OldETC/Bipedal_Qubie/faces/Untitled 1.gif

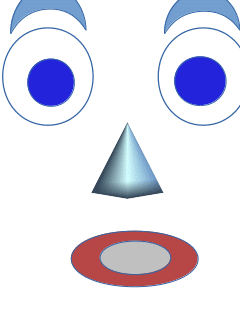
faces/Untitled 1.gif
