OldETC/Bipedal_Qubie/Qubie_code/python/faceClose.jpg

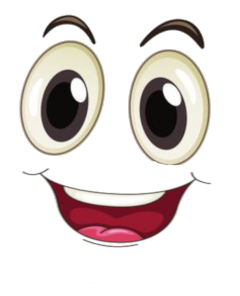
Qubie_code/python/faceClose.jpg
