OldETC/Bipedal_Qubie/qubie/stl/microgripper/connector.stl

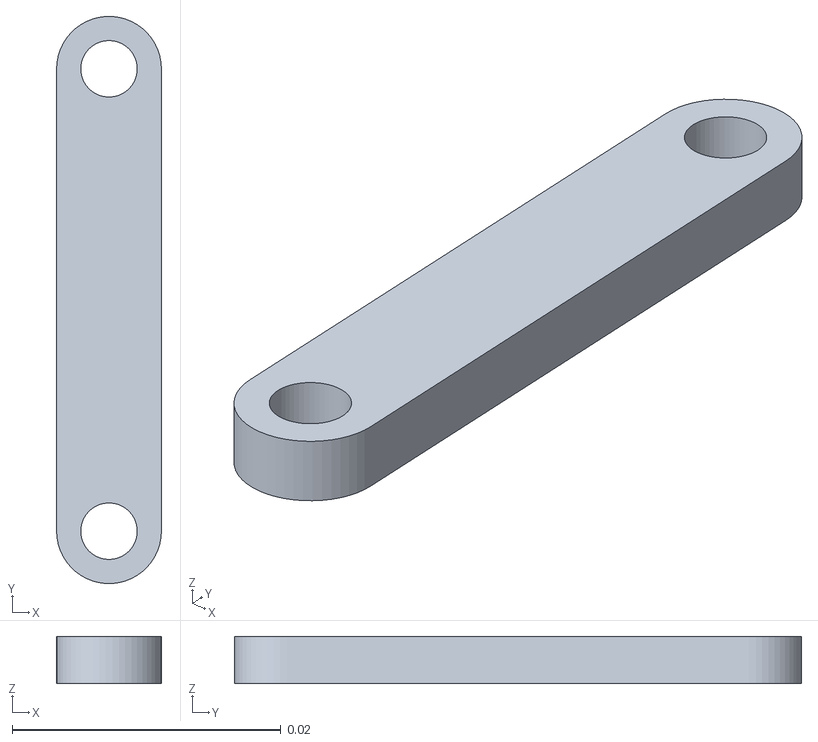
[picture p17: CAD file, 2021-06-25]
qubie/stl/microgripper/connector.stl
0.0078 x 0.0422 x 0.0035
