OldETC/Bipedal_Qubie/qubie/stl/minigripper/mybase.stl

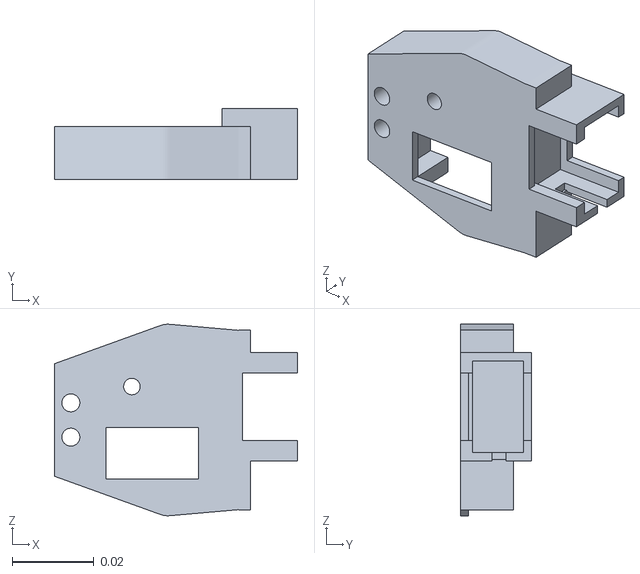
[picture p18: CAD file, 2021-06-25]
qubie/stl/minigripper/mybase.stl
0.0595 x 0.0174 x 0.0469
