OldETC/Bipedal_Qubie/PrintDesign/minigripper/minigripper/files/Connector.stl

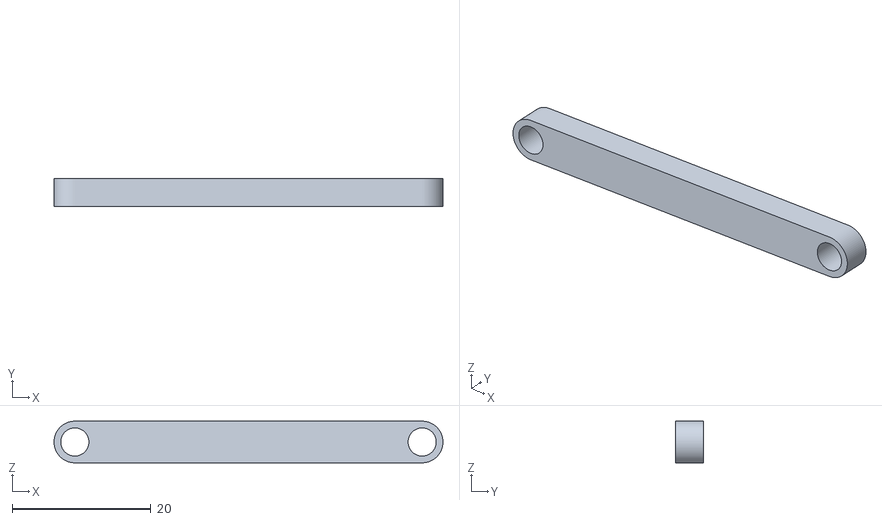
[picture p19: CAD file, 2021-06-24]
PrintDesign/minigripper/minigripper/files/Connector.stl
56.0 x 4.00 x 6.00
