OldETC/Bipedal_Qubie/qubie/stl/footassembly/shoe.stl

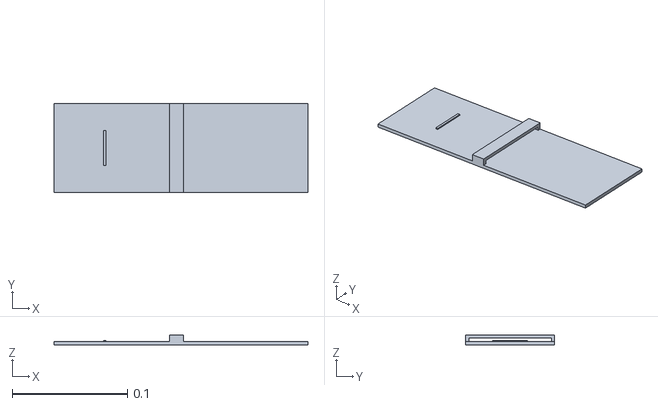
[picture p20: CAD file, 2021-06-25]
qubie/stl/footassembly/shoe.stl
0.22 x 0.0767 x 0.009
