OldETC/Bipedal_Qubie/qubie/stl/head/Neckclamp.stl

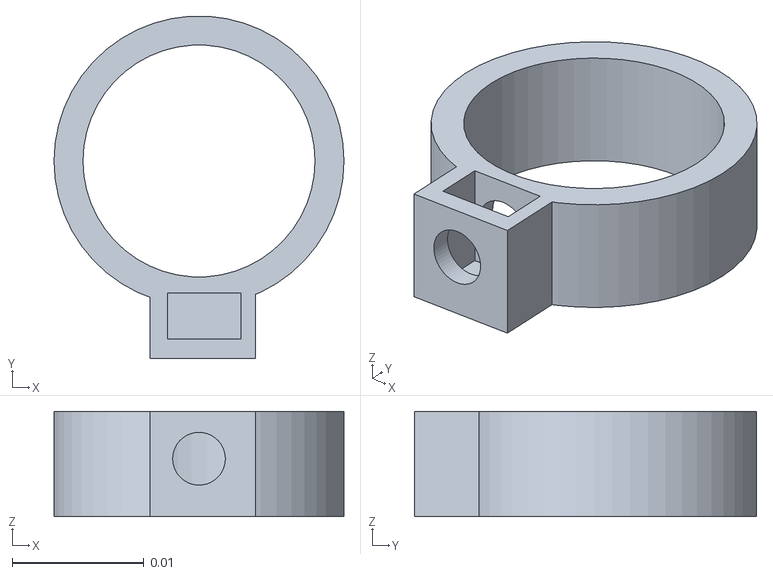
[picture p21: CAD file, 2021-06-25]
qubie/stl/head/Neckclamp.stl
0.022 x 0.026 x 0.008
