OldETC/Bipedal_Qubie/qubie/stl/microgripper/MountingPlate.stl

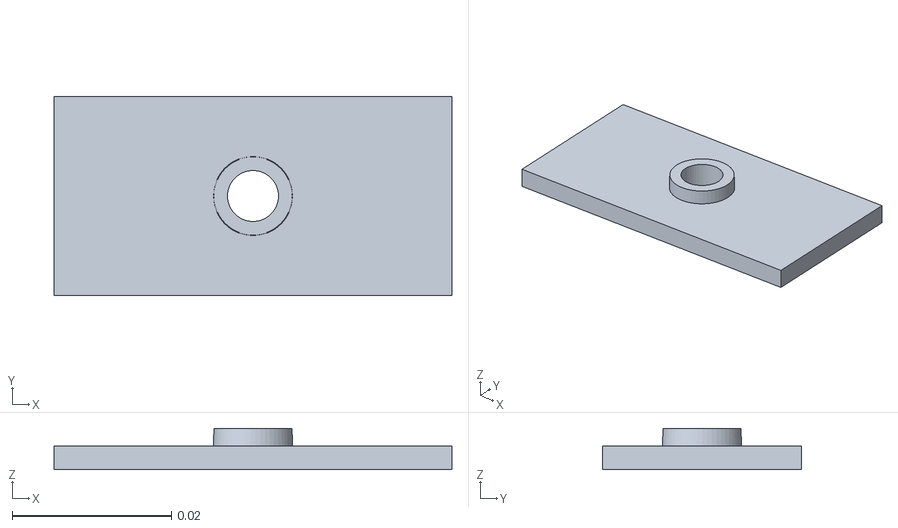
[picture p22: CAD file, 2021-06-25]
qubie/stl/microgripper/MountingPlate.stl
0.05 x 0.025 x 0.0052
