OldETC/Bipedal_Qubie/qubie/stl/minigripper/myminiclaw.stl

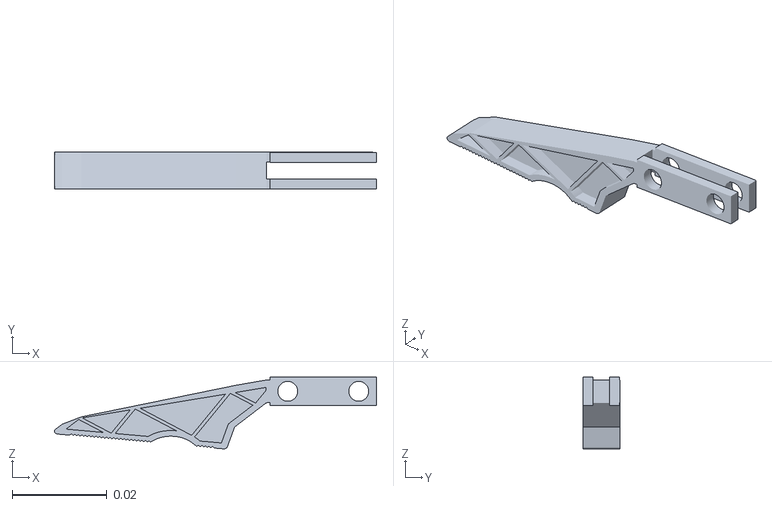
[picture p23: CAD file, 2021-06-25]
qubie/stl/minigripper/myminiclaw.stl
0.068 x 0.00774 x 0.0152
