OldETC/Bipedal_Qubie/PrintDesign/minigripper/minigripper/files/Base_AR2.stl

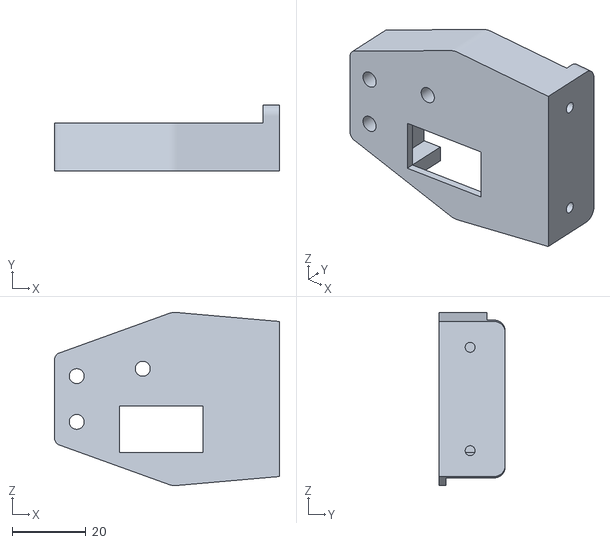
[picture p24: CAD file, 2021-06-24]
PrintDesign/minigripper/minigripper/files/Base_AR2.stl
61.0 x 18.0 x 46.9
