OldETC/Bipedal_Qubie/qubie/stl/gazeboLeftShoulderCrank.stl

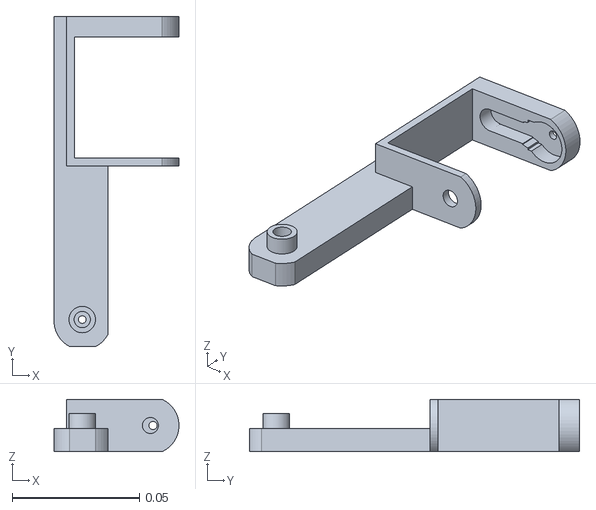
[picture p25: CAD file, 2021-06-25]
qubie/stl/gazeboLeftShoulderCrank.stl
0.0491 x 0.13 x 0.0205
