OldETC/Bipedal_Qubie/qubie/stl/head/Display.stl

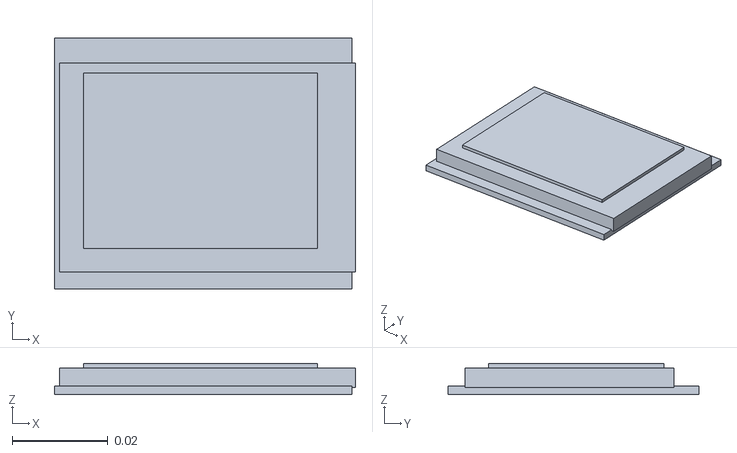
[picture p26: CAD file, 2021-06-25]
qubie/stl/head/Display.stl
0.063 x 0.0525 x 0.0065
