OldETC/Bipedal_Qubie/qubie/stl/minigripper/pivotplate.stl

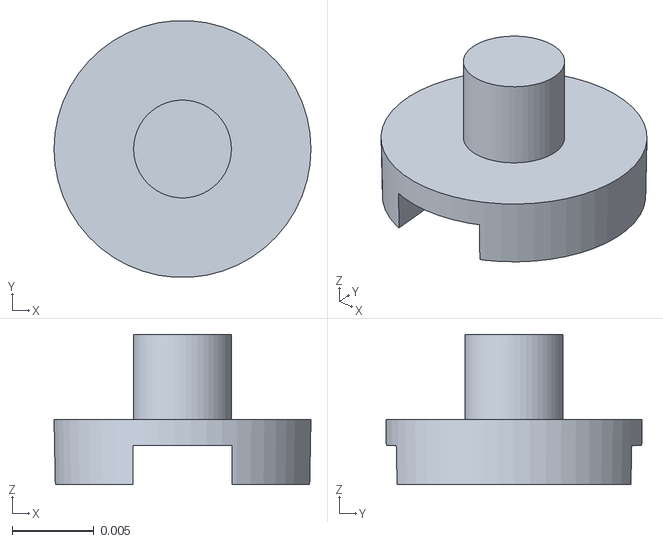
[picture p27: CAD file, 2021-06-25]
qubie/stl/minigripper/pivotplate.stl
0.0158 x 0.0157 x 0.0092
