OldETC/Bipedal_Qubie/qubie/stl/footassembly/gazeboRighttAnkleTilt.stl

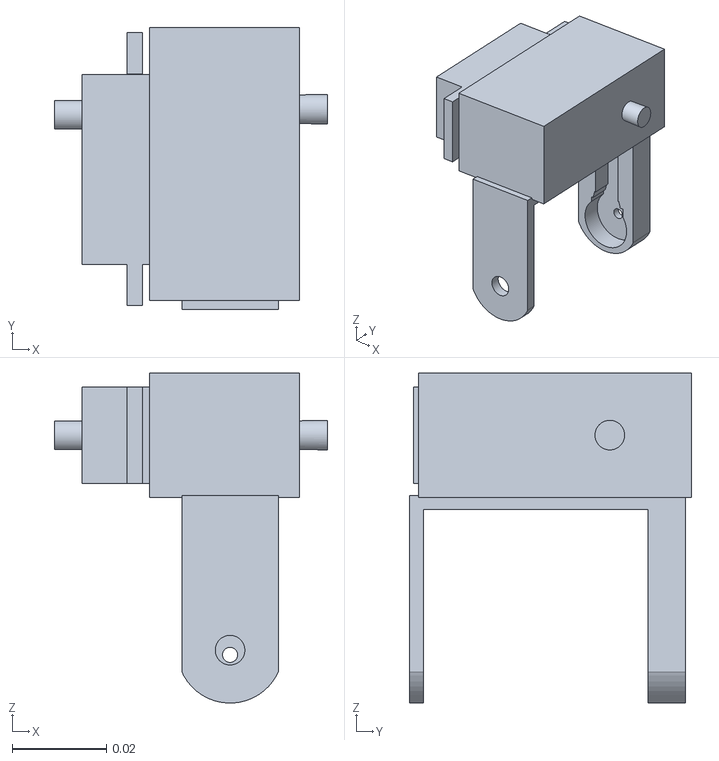
[picture p28: CAD file, 2021-06-25]
qubie/stl/footassembly/gazeboRighttAnkleTilt.stl
0.0581 x 0.06 x 0.0701
