OldETC/Bipedal_Qubie/qubie/stl/gazeboServoNbracket.stl

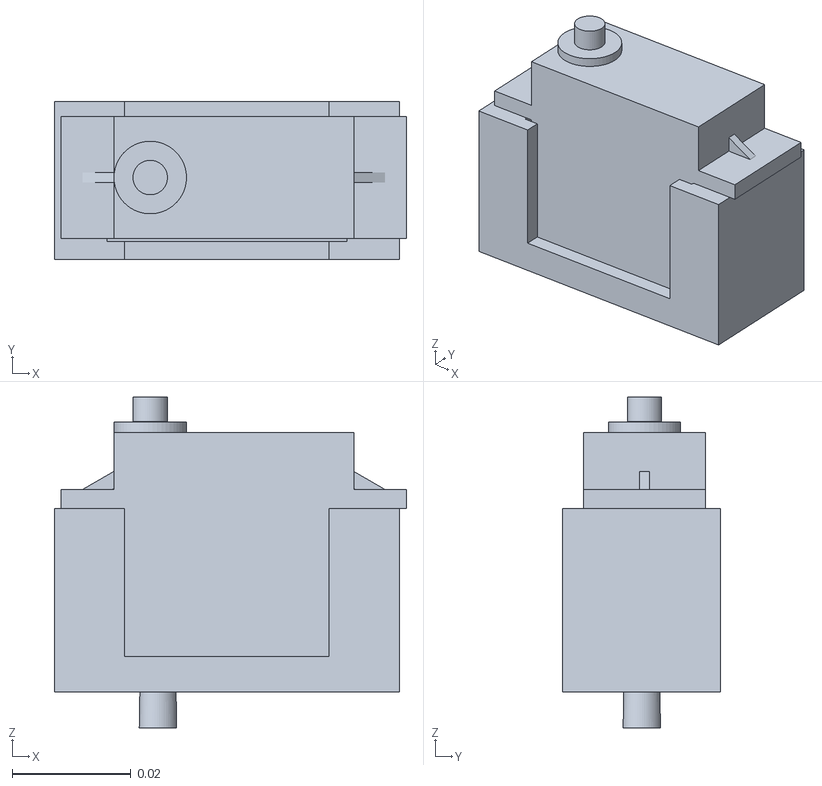
[picture p29: CAD file, 2021-06-25]
qubie/stl/gazeboServoNbracket.stl
0.0592 x 0.0265 x 0.0556
