OldETC/Bipedal_Qubie/qubie/stl/head/SpinPlatform.stl

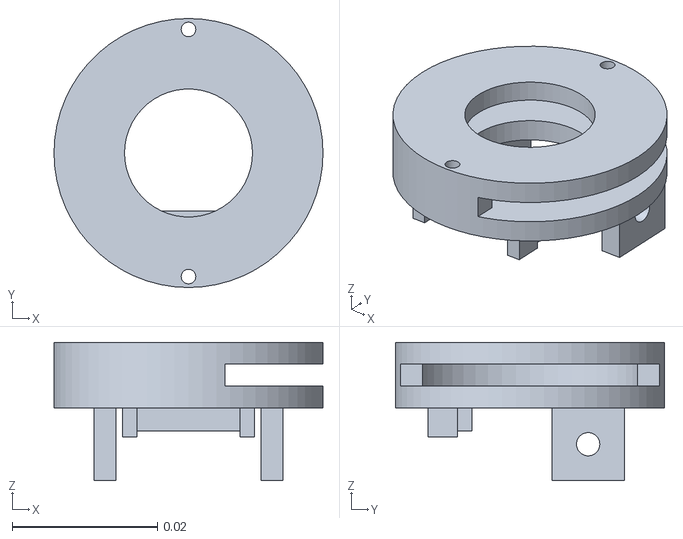
[picture p30: CAD file, 2021-06-25]
qubie/stl/head/SpinPlatform.stl
0.037 x 0.037 x 0.019
