OldETC/Bipedal_Qubie/qubie/stl/microgripper/PivotPlateCap.stl

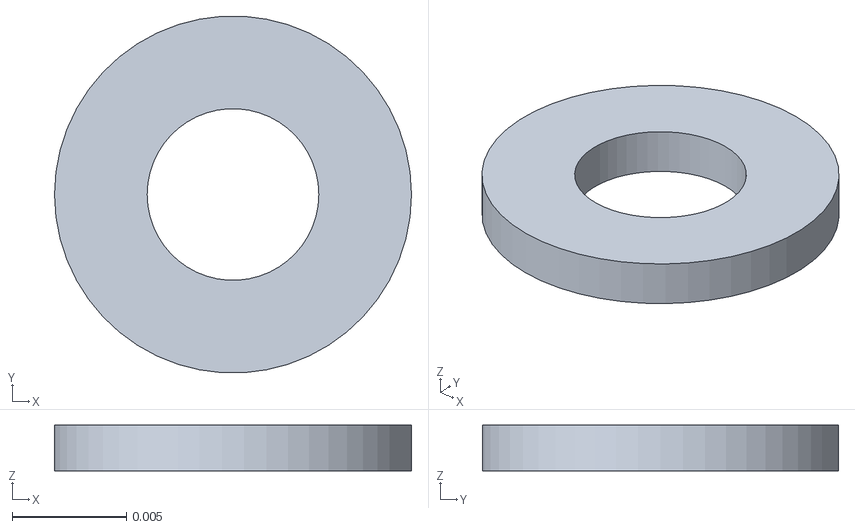
[picture p31: CAD file, 2021-06-25]
qubie/stl/microgripper/PivotPlateCap.stl
0.0156 x 0.0156 x 0.002
