OldETC/Bipedal_Qubie/qubie/stl/minigripper/myclaw.stl

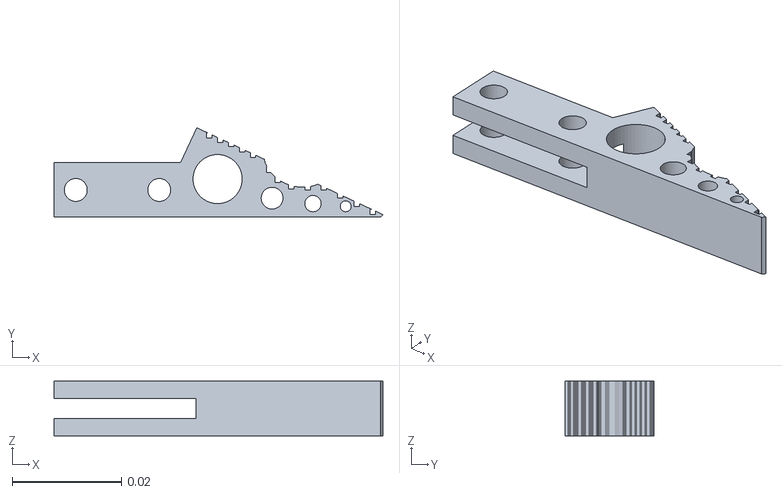
[picture p32: CAD file, 2021-06-25]
qubie/stl/minigripper/myclaw.stl
0.0603 x 0.0164 x 0.01
