OldETC/Bipedal_Qubie/qubie/stl/footassembly/robotFoot.stl

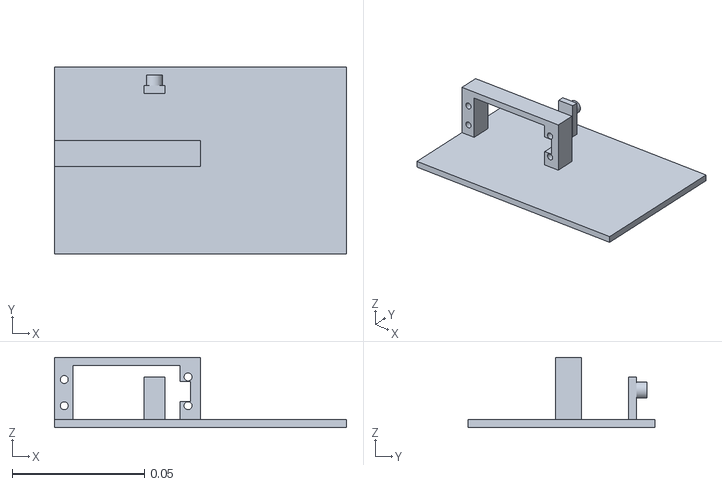
[picture p33: CAD file, 2021-06-25]
qubie/stl/footassembly/robotFoot.stl
0.11 x 0.0707 x 0.0266
