OldETC/Bipedal_Qubie/qubie/stl/head/headBack.stl

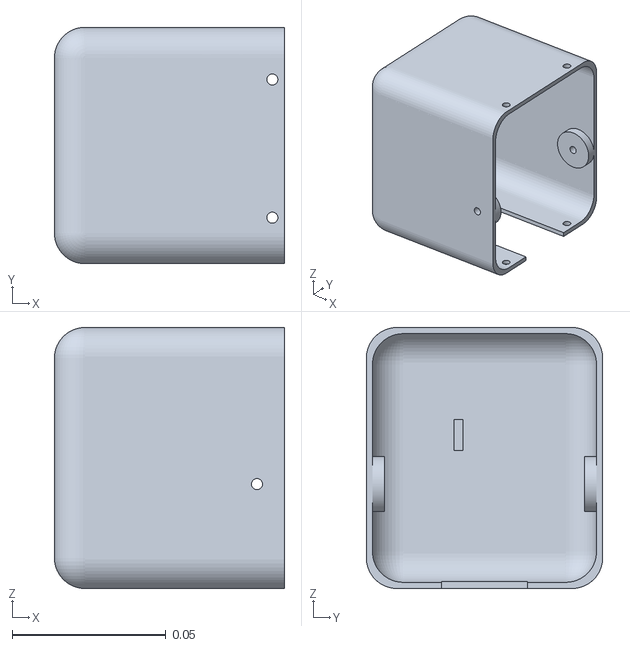
[picture p34: CAD file, 2021-06-25]
qubie/stl/head/headBack.stl
0.075 x 0.077 x 0.085
