OldETC/Bipedal_Qubie/qubie/stl/head/NeckStem.stl

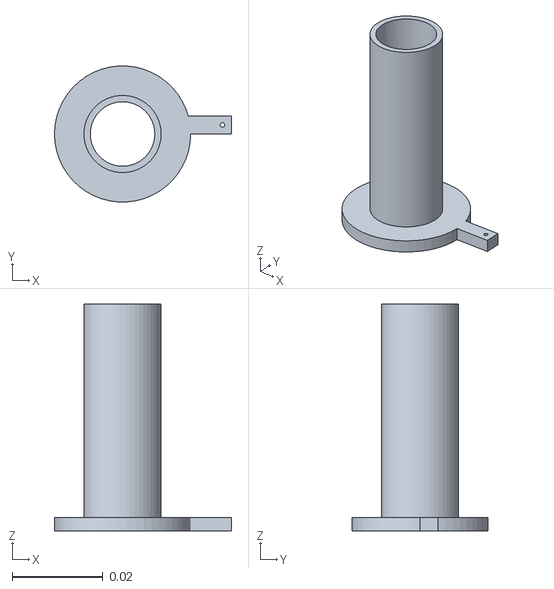
[picture p35: CAD file, 2021-06-25]
qubie/stl/head/NeckStem.stl
0.039 x 0.0299 x 0.05
