OldETC/Bipedal_Qubie/qubie/stl/DS3218.stl

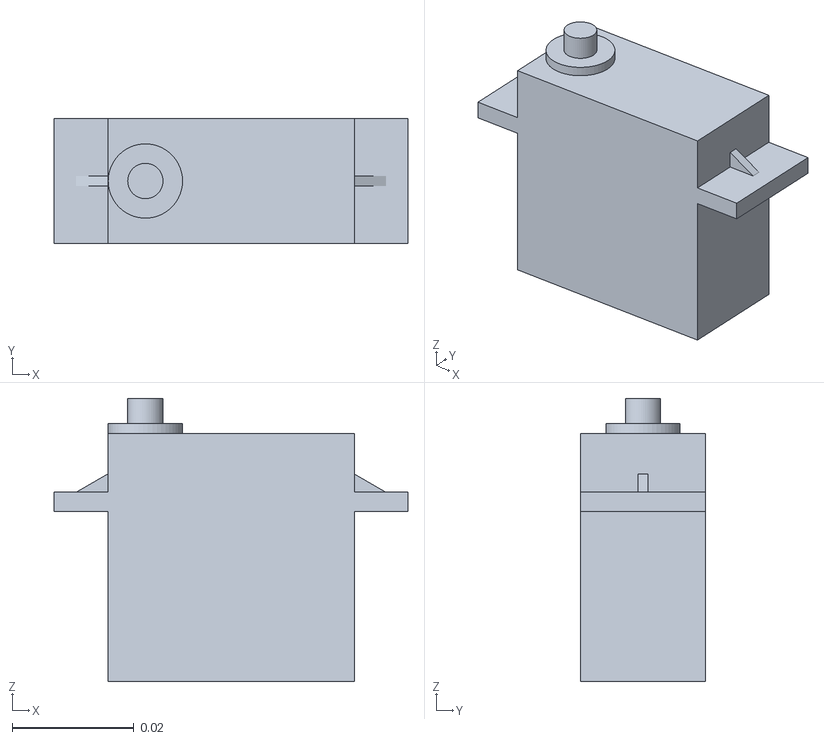
[picture p36: CAD file, 2021-06-25]
qubie/stl/DS3218.stl
0.0581 x 0.0205 x 0.0465
