OldETC/Bipedal_Qubie/qubie/stl/head/headtiltshaft.stl

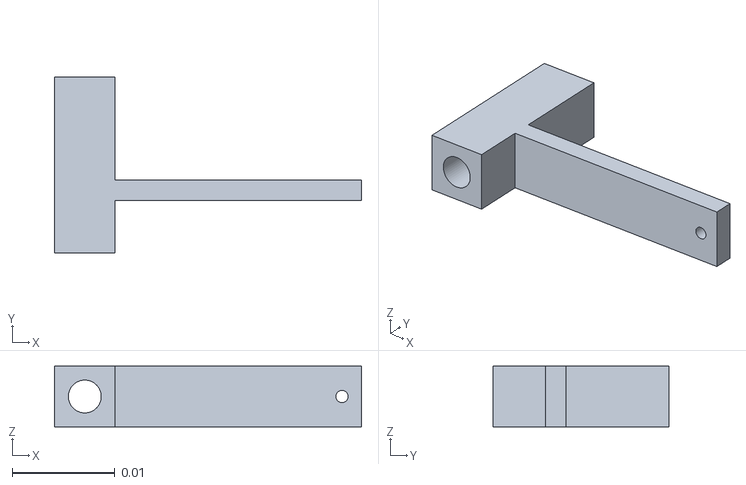
[picture p37: CAD file, 2021-06-25]
qubie/stl/head/headtiltshaft.stl
0.0299 x 0.0171 x 0.0059
