OldETC/Bipedal_Qubie/qubie/stl/head/DisplayBezel.stl

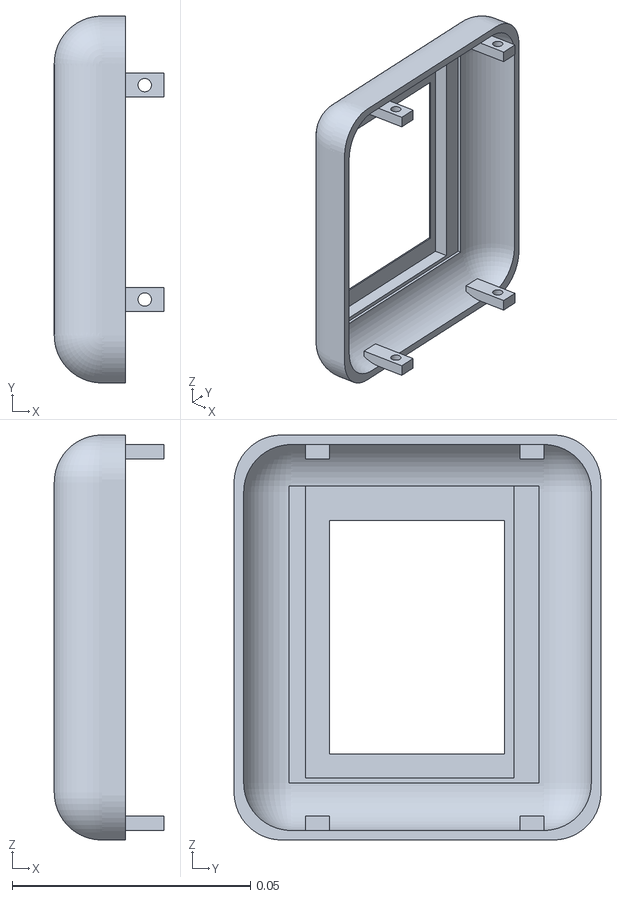
[picture p38: CAD file, 2021-06-25]
qubie/stl/head/DisplayBezel.stl
0.023 x 0.077 x 0.085
