OldETC/Bipedal_Qubie/qubie/stl/gazeboHead.stl

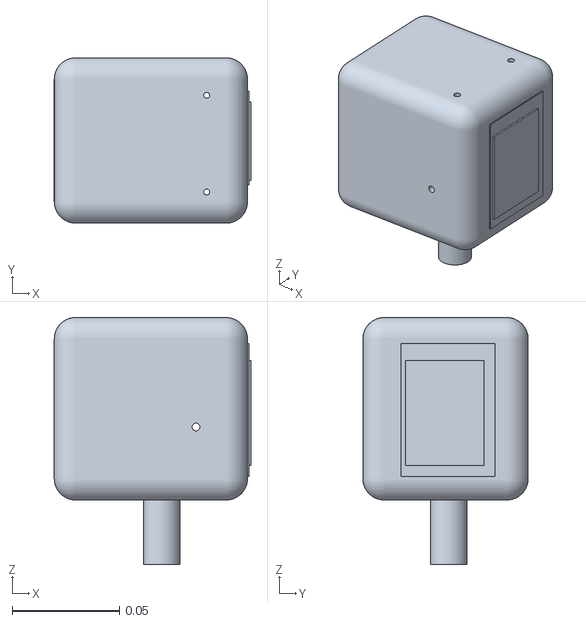
[picture p39: CAD file, 2021-06-25]
qubie/stl/gazeboHead.stl
0.0915 x 0.077 x 0.115
