OldETC/Bipedal_Qubie/qubie/stl/gazeboLeftAnkleRoll.stl

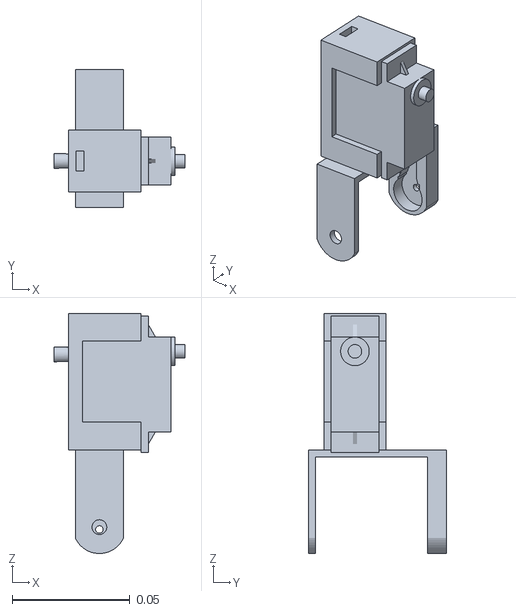
[picture p40: CAD file, 2021-06-25]
qubie/stl/gazeboLeftAnkleRoll.stl
0.0556 x 0.0587 x 0.102
