OldETC/Bipedal_Qubie/qubie/stl/bodycover.stl

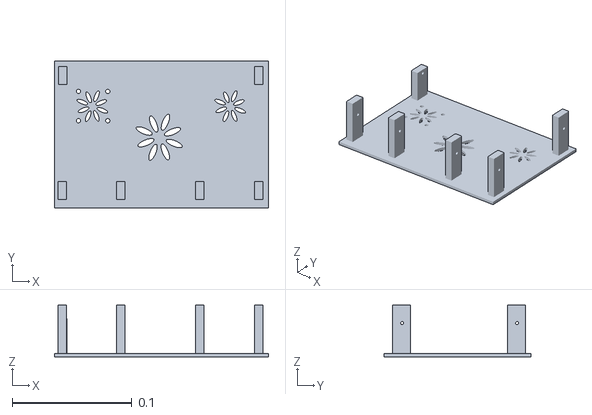
[picture p41: CAD file, 2021-06-25]
qubie/stl/bodycover.stl
0.179 x 0.123 x 0.0432
