OldETC/Bipedal_Qubie/qubie/stl/pivotingservobracket.stl

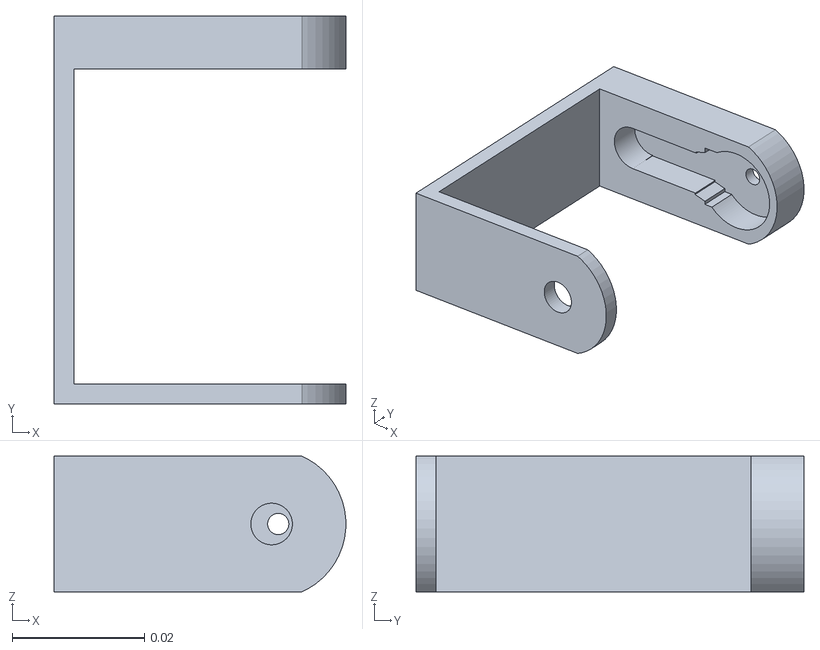
[picture p42: CAD file, 2021-06-25]
qubie/stl/pivotingservobracket.stl
0.0441 x 0.0587 x 0.0205
