OldETC/Bipedal_Qubie/qubie/stl/gazebobracketpair.stl

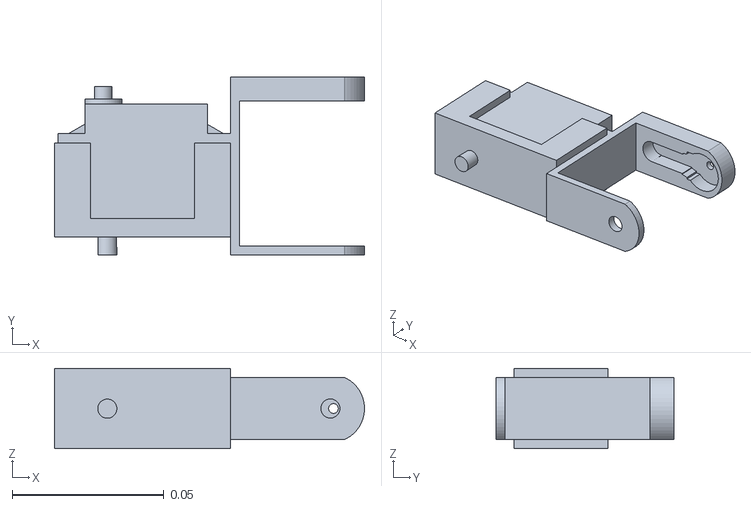
[picture p43: CAD file, 2021-06-25]
qubie/stl/gazebobracketpair.stl
0.102 x 0.0587 x 0.0265
