OldETC/Bipedal_Qubie/qubie/stl/neckExtension.stl

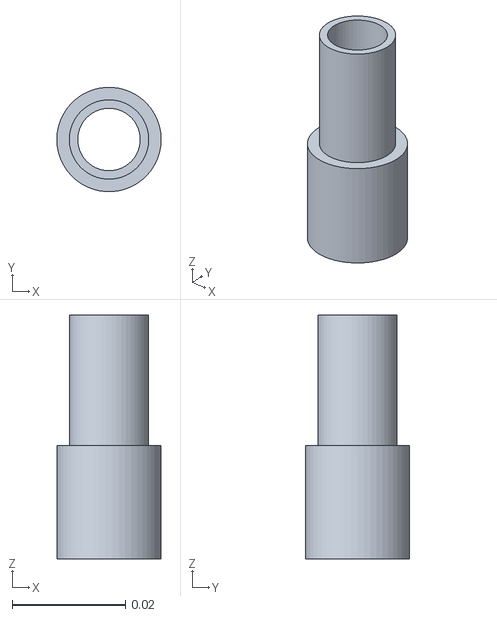
[picture p44: CAD file, 2021-06-25]
qubie/stl/neckExtension.stl
0.0184 x 0.0184 x 0.043
