OldETC/Bipedal_Qubie/qubie/stl/gazeboLeftHipPivot.stl

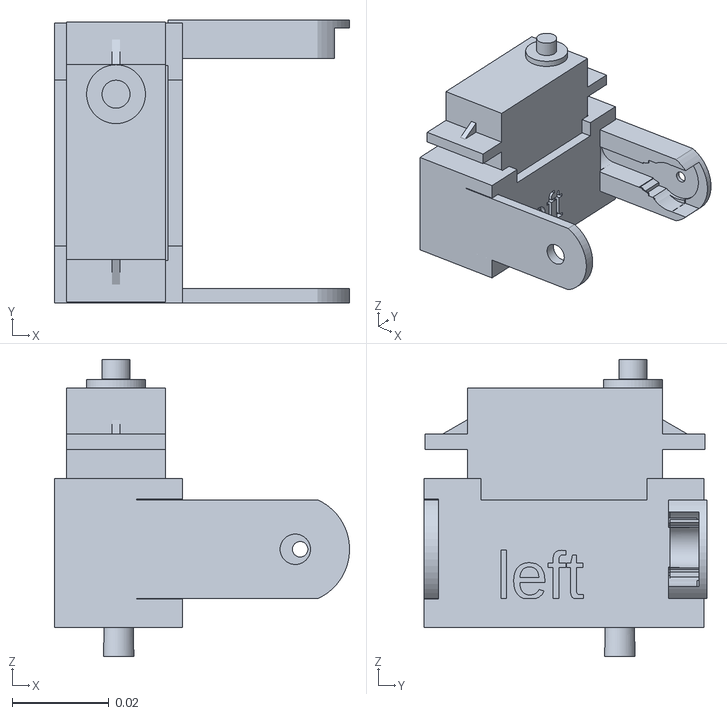
[picture p45: CAD file, 2021-06-25]
qubie/stl/gazeboLeftHipPivot.stl
0.0611 x 0.0587 x 0.0616
