OldETC/Bipedal_Qubie/qubie/stl/gazeboLeftFoot.stl

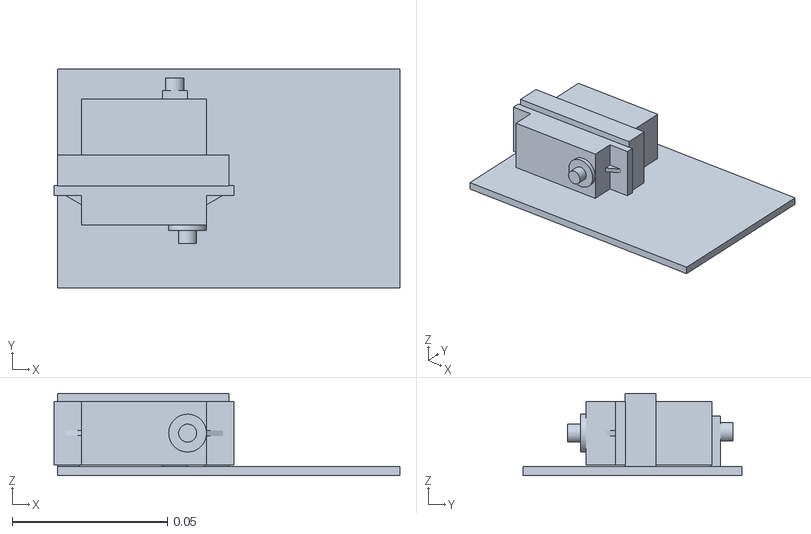
[picture p46: CAD file, 2021-06-25]
qubie/stl/gazeboLeftFoot.stl
0.112 x 0.0707 x 0.0266
