OldETC/Bipedal_Qubie/qubie/stl/gazeboServoBlock.stl

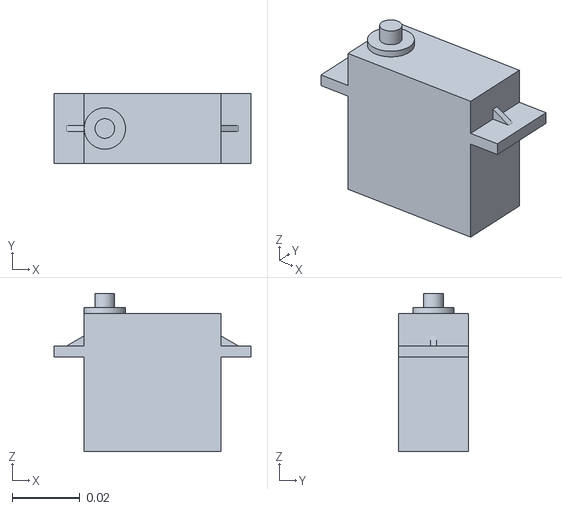
[picture p47: CAD file, 2021-06-25]
qubie/stl/gazeboServoBlock.stl
0.0581 x 0.0205 x 0.0466
