OldETC/Bipedal_Qubie/qubie/stl/iShoulder.stl

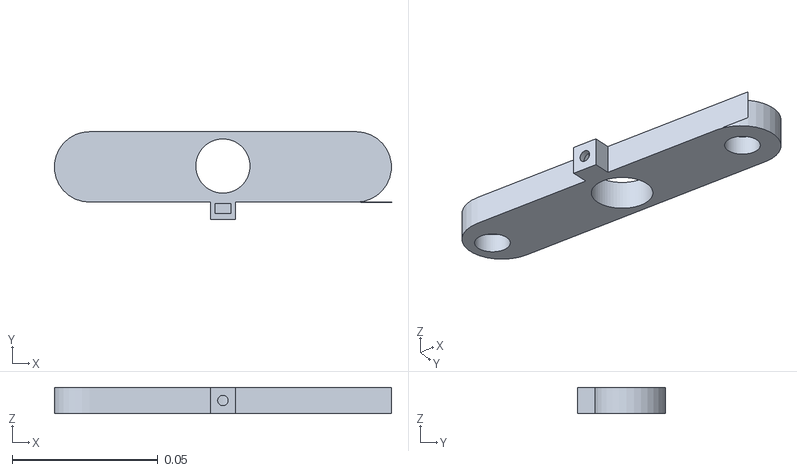
[picture p48: CAD file, 2021-06-25]
qubie/stl/iShoulder.stl
0.116 x 0.0301 x 0.009
