OldETC/Bipedal_Qubie/qubie/stl/gazeboRightHipPivot.stl

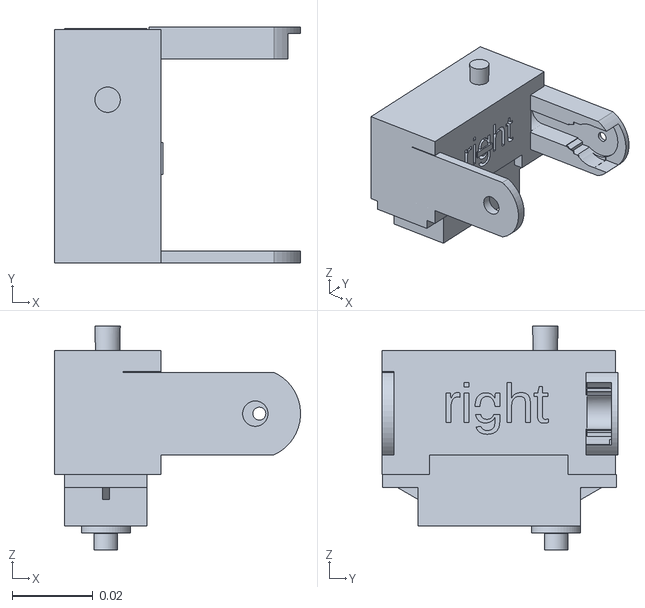
[picture p49: CAD file, 2021-06-25]
qubie/stl/gazeboRightHipPivot.stl
0.0611 x 0.0587 x 0.0556
