OldETC/Bipedal_Qubie/PrintDesign/headassy/neckAssyMech.png

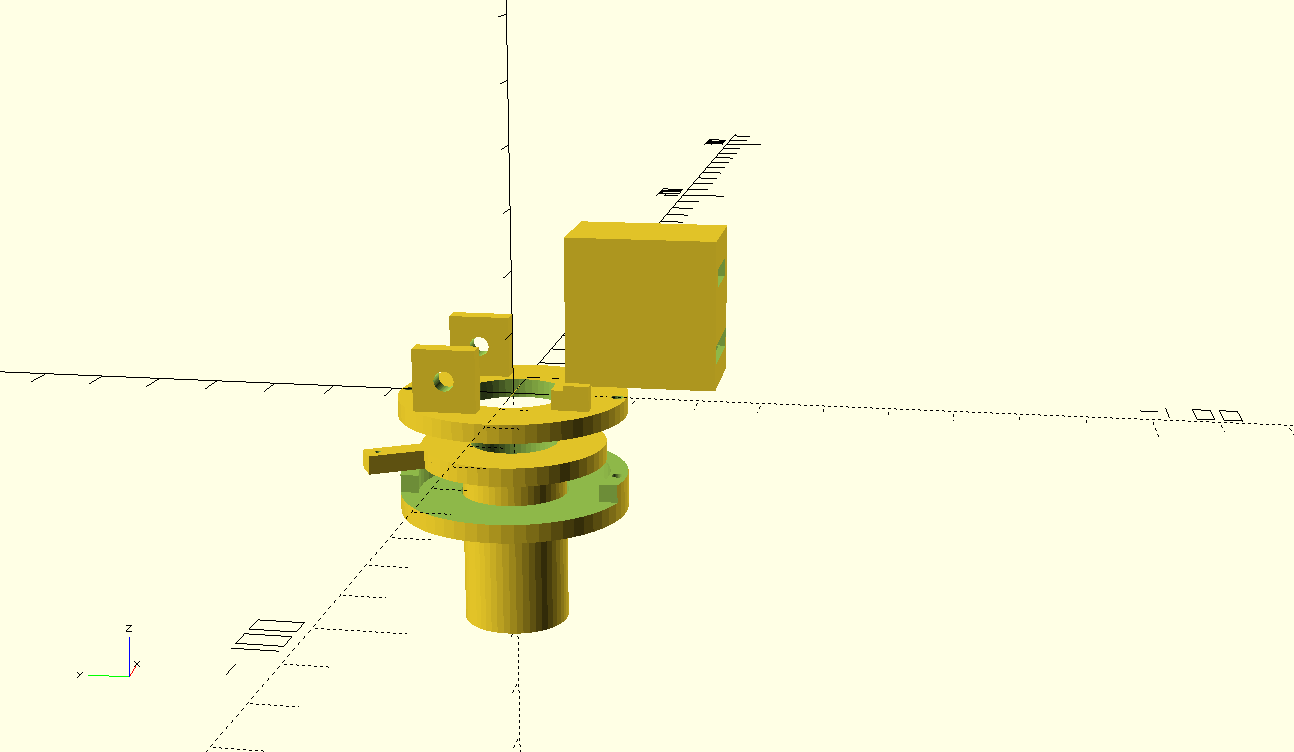
PrintDesign/headassy/neckAssyMech.png
